geezacoleman/owl-driver-board/doc/4-v2.4/2.jpg

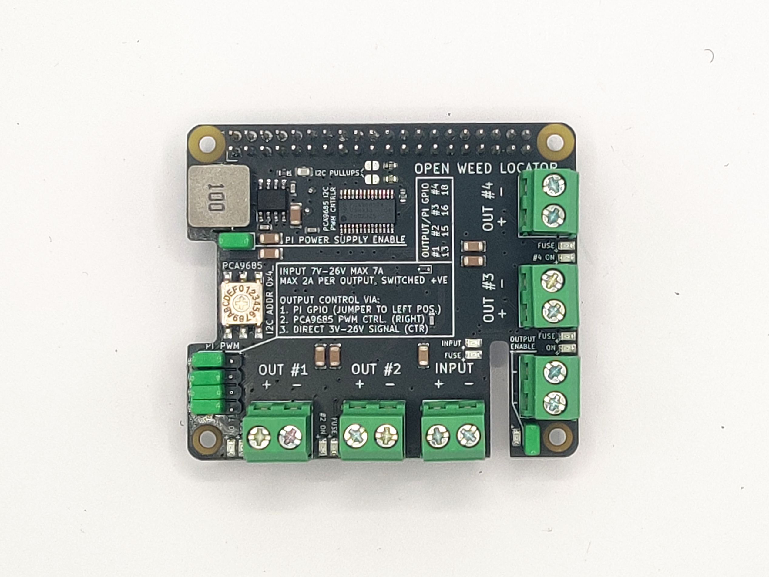
doc/4-v2.4/2.jpg
