geezacoleman/owl-driver-board/doc/16-v1.0/5.jpg

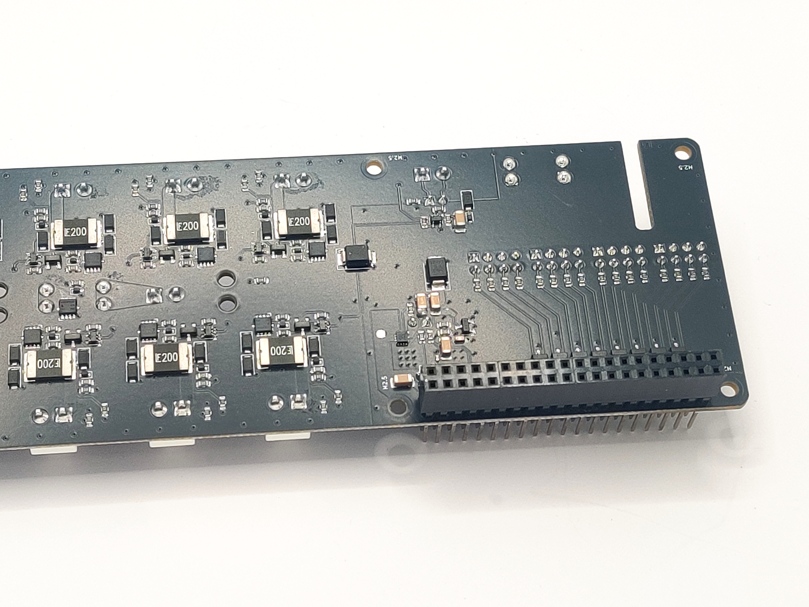
doc/16-v1.0/5.jpg
